famulus/rainboard/website/img/rainboard-midi-controller.jpeg

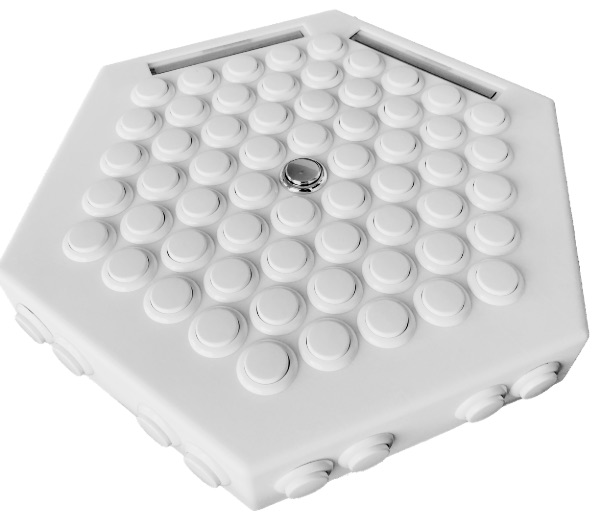
website/img/rainboard-midi-controller.jpeg
